GarettMorrison/DrawBot/DrawBoi_Dated/drawBoi/steps.h

#ifndef _steps_H 
#define _steps_H 
#include <Arduino.h> 
#include <avr/pgmspace.h> 
#define number_of_steps 9449 
static int stepCount = number_of_steps; 
static const PROGMEM byte steps[number_of_steps] = { 
	0,
	0,
	0,
	0,
	0,
	0,
	0,
	0,
	0,
	0,
	0,
	0,
	0,
	0,
	0,
	0,
	0,
	0,
	0,
	0,
	0,
	0,
	0,
	0,
	0,
	0,
	0,
	0,
	0,
	0,
	0,
	0,
	0,
	0,
	0,
	0,
	0,
	0,
	0,
	0,
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
}; 
#endif //_steps_H 
